cipz/ArduTracker/essay/charts/ble-indoor-outdoor.png

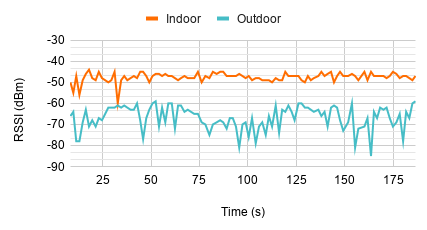
essay/charts/ble-indoor-outdoor.png
