cipz/ArduTracker/essay/charts/ble-moving-station-indoor-outdoor.png

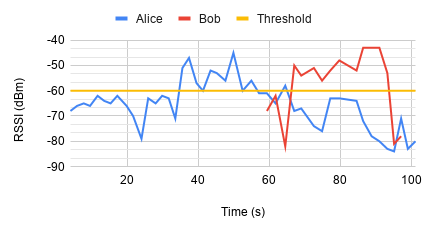
essay/charts/ble-moving-station-indoor-outdoor.png
