cipz/ArduTracker/essay/charts/rf24-long-short-2mbps.png

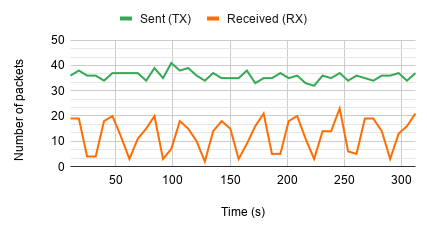
essay/charts/rf24-long-short-2mbps.png
