cipz/ArduTracker/essay/charts/rf24-long-short-250kbps.png

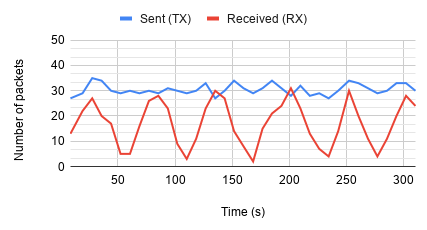
essay/charts/rf24-long-short-250kbps.png
