cipz/ArduTracker/essay/schemas/case-study-workflow.png

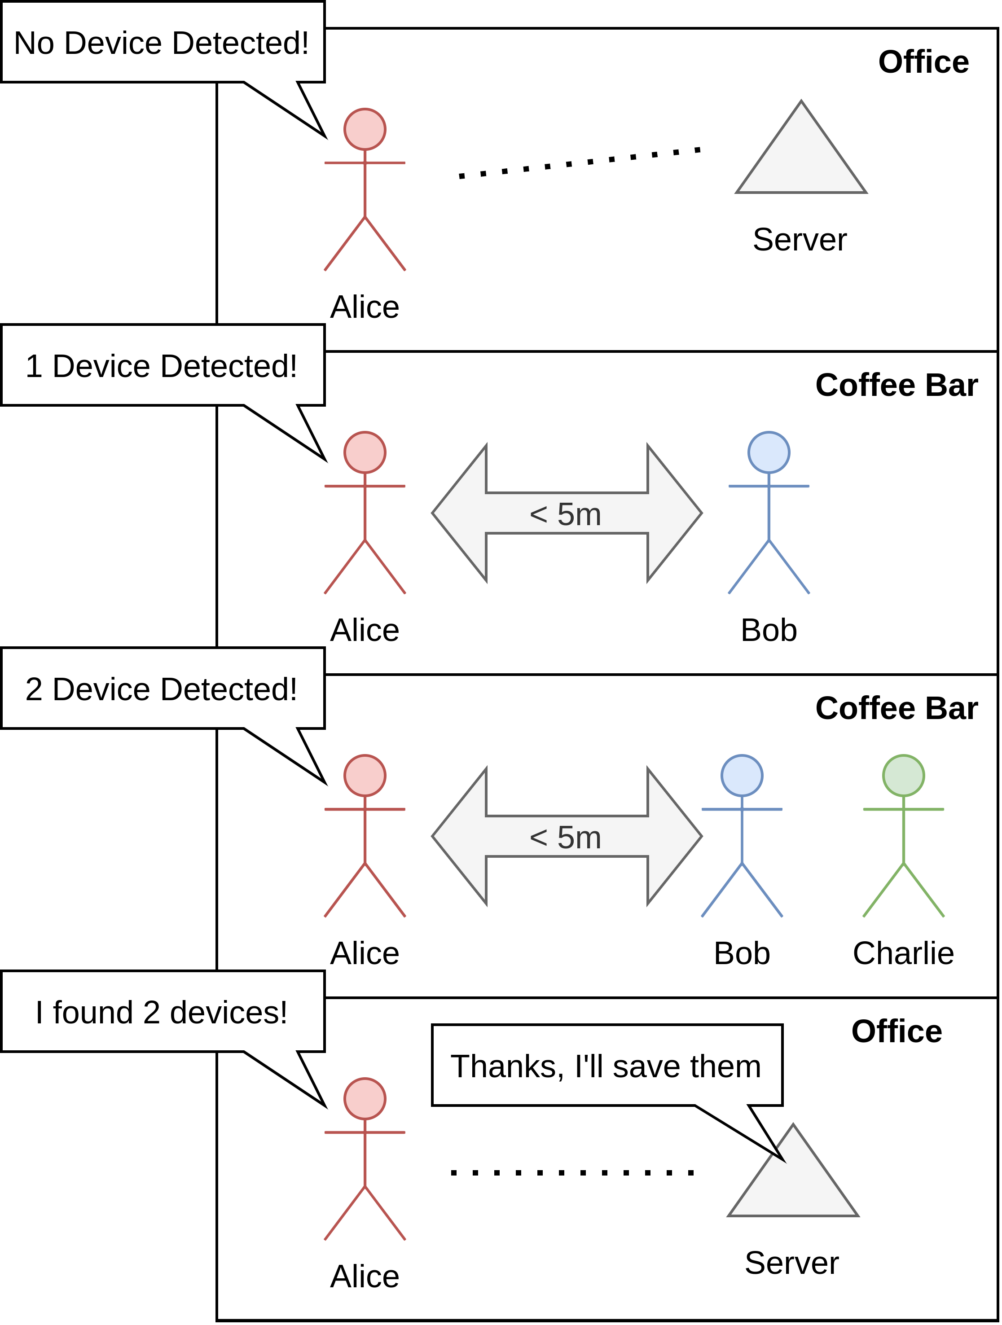
essay/schemas/case-study-workflow.png
