cipz/ArduTracker/essay/schemas/exposure-workflow.png

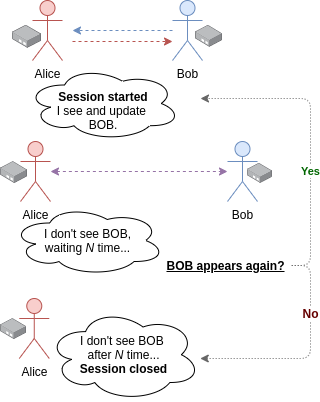
essay/schemas/exposure-workflow.png
