cipz/ArduTracker/essay/schemas/graph-moving-2stations.png

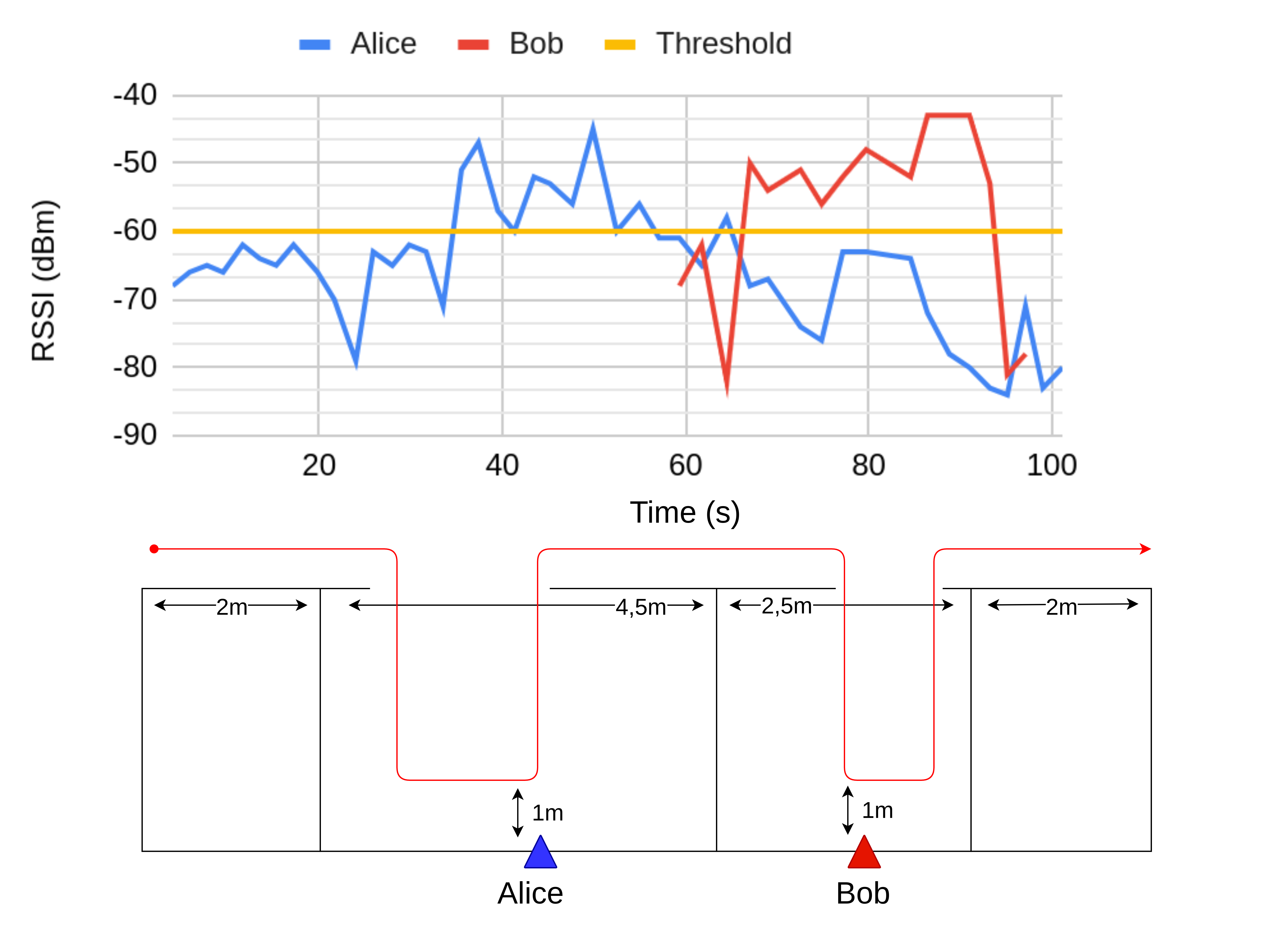
essay/schemas/graph-moving-2stations.png
