cipz/ArduTracker/essay/schemas/graph-moving-station.png

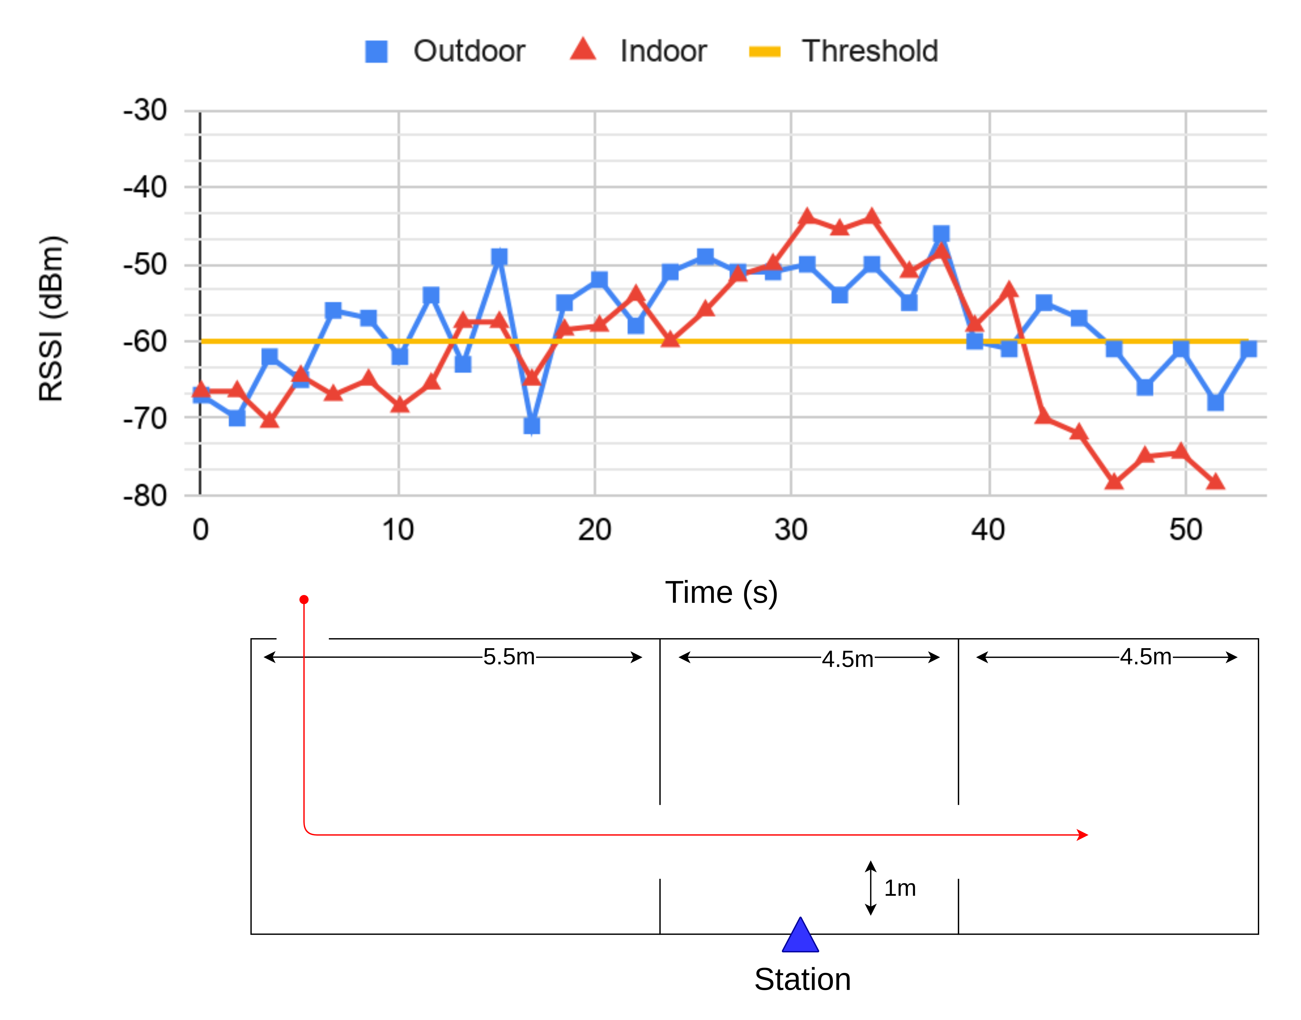
essay/schemas/graph-moving-station.png
