cipz/ArduTracker/ArduTracker/src/at_ble.h

/*
 *  BLE Module functions
 *  --------
 *  This file contains all the functions relative to the radio controls in order to
 *  send and receive messages between multiple prototypes
*/

#pragma once
#include "abstract_radio.h"
#include <BLEDevice.h>
#include <BLEServer.h>
#include <BLEUtils.h>
// --------------------------------------- BLE Controller

#define BLE_NAME "ArduTracker_ESP32"
#define SERV_UUID "e96bf93a-79b0-11eb-9439-0242ac130002" //random-generated

int newFriendsCount;

/**
 *  Util: converts std::string to String
*/
String stdToString(std::string str) {
    String res = "";
    for(int i=0; i<str.size(); i++)
        res += str[i];
    return res;
}

class BLEController : public AbsRadioController{
    int randomRxTime = random(RANDOM_TX_MILLS_MIN, RANDOM_TX_MILLS_MAX);
    int randomTxTime = random(RANDOM_RX_MILLS_MIN, RANDOM_RX_MILLS_MAX);

    int statsTx = 0;
    int statsRx = 0;

    BLEScan* pBLEScan;  

    public: 
    /**
     * Initialize radio parameters
    */
    void init() override {
        Serial.println("Initializing BLE functions");

        //Start BLE Server
        BLEDevice::init(BLE_NAME);
        BLEServer *pServer = BLEDevice::createServer();

        if(!params.station_mode) {
            // Setup Payload attached to the advertisement with my_id
            BLEAdvertisementData pAdvertisementData = BLEAdvertisementData();
            pAdvertisementData.setFlags(0x04); // BR_EDR_NOT_SUPPORTED (to hide Standard Bluetooth Connection)
            char nameToSend[18] = BLE_PREFIX;
            strcat(nameToSend, params.my_id);
            pAdvertisementData.setServiceData(BLEUUID(SERV_UUID), nameToSend);

            // Advertise BLE Server readiness
            BLEAdvertising *pAdvertising = pServer->getAdvertising();
            pAdvertising->setAdvertisementData(pAdvertisementData);
            pAdvertising->start();
        }
        
        // Initialize BLE scanning
        pBLEScan = BLEDevice::getScan();
        pBLEScan->setActiveScan(true);
    }

    /**
     * Scan for other BLE devices
     * @return the number of new friends found
    */
    LinkedList<Log>* scan() override {
        LinkedList<Log>* newFriends = new LinkedList<Log>();

        int scanDuration = params.scan_duration/1000;
        BLEScanResults devices = pBLEScan->start(scanDuration); 

        this->statsRx = 0;

        for(int i=0; i<devices.getCount(); ++i){
            BLEAdvertisedDevice advertisedDevice = devices.getDevice(i);

            if(DEBUG_MODE) {
                Serial.printf(
                    "Found: %s >> %s [%s] RSSI:%d\n",
                    advertisedDevice.getName().c_str(),
                    advertisedDevice.getServiceData().c_str(),
                    advertisedDevice.getAddress().toString().c_str(),
                    advertisedDevice.getRSSI());
            }

                            
            String name = String(advertisedDevice.getServiceData().c_str());
            String prefix = name.substring(0, 3);
            String suffix = name.substring(3, name.length());

            if(prefix.equals(BLE_PREFIX)){
                int rssi = advertisedDevice.getRSSI();

                if(rssi > params.ble_threshold) {
                    newFriends->add(Log(suffix.c_str(), rssi));
                    this->statsRx = rssi; //FIXME: in case of multiple defices, it saves just the last rssi
                }
            }
        }
        return newFriends;
    }

    void send(){
        return;
    }

    int getStatsTx() override{
        return this->statsTx;
    }

    int getStatsRx() override{
        return this->statsRx;
    }
};
