cipz/ArduTracker/ArduTracker/src/at_log.h

/*
 *  Log class
 *  --------
 *  This file contains the class that describes a single log record between 2 subjects
*/
#pragma once
#include <time.h>

#define RSSI_ERROR_TOLERANCE 20 //[bD]

// --------------------------------------- Log class data structure

class Log {
public:
    char friend_id[15];
    double rssi;
    unsigned long start_millis;
    unsigned long end_millis;
    time_t last_exposure_time;
    
    unsigned int cycle_counter;
    bool is_from_cache;
    double prev[2] = {0, 0};
    double prev_mean[2] = {0, 0};

    Log(const char * fi = "Default", double rssi = 0.0, unsigned long sm = millis()-1000, unsigned long em = millis(), time_t let = time(nullptr), bool ifc = false) {

        strlcpy(this->friend_id, fi, sizeof(this->friend_id));
        this->rssi = rssi;
        this->start_millis = sm;
        this->end_millis = em;
        this->last_exposure_time = let;
        this->cycle_counter = 1;
        this->is_from_cache = ifc;
    }

    Log(StaticJsonDocument<1024> jsonData, bool ifc = true) {
        this->unserializeLocal(jsonData);
        this->is_from_cache = ifc;
    }

    long getExposureMillis() const {
        return end_millis - start_millis;
    }

    void updateExposureSession(double rssi = 0.0){
        
        // OLD: critical cases to fix
        /* Note: time without a proper config counts the seconds since the start of the board
         * Note 2: 1year = 31546000, aleatory value for sanity check
         *
         * Critical case: the exposure session start before time alignment and the new  time is much more greater.
         * 1. Se lastExposureTime < time(nullptr) - 31546000
         * newLastExposureTime = lastExposureTime + time(nullptr) 
         * 
         * Critical case: the exposure session resumes after a restart and the time is not correct yet due to wifi disconnection
         * 2. Se firstExposureTime < time(nullptr) - 31546000 
         * newFirstExposureTime = firstExposureTime - time(nullptr)
        */

        if(this->is_from_cache) {
            return;
        }

        this->end_millis = millis();
        this->last_exposure_time = time(nullptr);
        this->cycle_counter++;

        if(DEBUG_MODE) { 
            Serial.println("\nMEAN:");
            Serial.printf("OLD:%f RSSIs:%f\t%f\t%f \n", this->rssi, prev[0], prev[1], rssi);
        }

        // Error control
        if(prev[0] && prev[1]) {
            double new_value = (prev[0] + rssi) / 2;

            if(abs(prev[1] - new_value) > RSSI_ERROR_TOLERANCE) {
                prev[1] = new_value;

                //restore the previous mean
                this->rssi = prev_mean[0];

                //add the re-calculated value
                this->rssi = this->rssi + ((new_value - this->rssi) / (this->cycle_counter - 1)); 
            }
        }
        
        this->rssi = this->rssi + ((rssi - this->rssi) / this->cycle_counter); // rssi average calculation

        if(DEBUG_MODE)
            Serial.printf("NEW:%f \n\n",this->rssi);

        if(STATS_DEBUG_MODE && prev[1]){
            stats[0] = rssi;
            stats[1] = prev[1];
        }

        //update prevs
        prev[0] = prev[1];
        prev[1] = rssi;
        prev_mean[0] = prev_mean[1];
        prev_mean[1] = this->rssi;
    }

    void unserializeLocal(StaticJsonDocument<1024> jsonData) {
        strlcpy(this->friend_id, jsonData["friend_id"], sizeof(this->friend_id));
        this->rssi = jsonData["rssi"];
        char tmpSm[32];
        char tmpEm[32];
        char tmpLastExpTime[32];
        strlcpy(tmpSm, jsonData["start_millis"], sizeof(tmpSm));
        strlcpy(tmpEm, jsonData["end_millis"], sizeof(tmpEm));
        strlcpy(tmpLastExpTime, jsonData["last_exposure_time"], sizeof(tmpLastExpTime));
        this->start_millis = strtol(tmpSm, nullptr, 10);
        this->end_millis = strtol(tmpEm, nullptr, 10); 
        this->last_exposure_time = (time_t) strtol(tmpLastExpTime, nullptr, 10); 
        this->cycle_counter = jsonData["cycle_counter"];
    }

    String serializeLocal() const {
        String msg = "{";
        msg += "\"friend_id\": \""    + (String)this->friend_id + "\",";
        msg += "\"start_millis\": \"" + (String)this->start_millis + "\",";
        msg += "\"end_millis\": \"" + (String)this->end_millis + "\",";
        msg += "\"last_exposure_time\": \"" + (String)this->last_exposure_time + "\",";
        msg += "\"rssi\": "         + (String)this->rssi + ",";
        msg += "\"cycle_counter\": "   + (String)this->cycle_counter;
        msg += "}";

        return msg;
    }

    String serializeMqtt(const char * my_id = params.my_id) const {
        String msg = "{";
        msg += "\"my_id\": \""        + (String)my_id   + "\",";
        msg += "\"friend_id\": \""    + (String)this->friend_id + "\",";
        msg += "\"seen_millis\": \""  + (String)this->getExposureMillis() + "\",";
        msg += "\"seen_time\": \""    + (String)this->last_exposure_time + "\",";
        msg += "\"rssi\": \""         + (String)this->rssi + "\",";
        msg += "\"scan_count\": \""   + (String)this->cycle_counter + "\"";
        msg += "}";

        return msg;
    }
};
